pepaslabs/HeadlightRelayControl/github media/Clipboard08.png

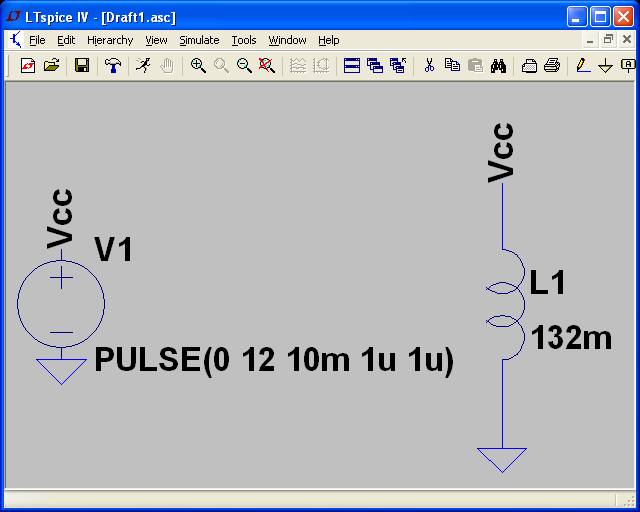
github media/Clipboard08.png
