pepaslabs/HeadlightRelayControl/github media/Clipboard13.png

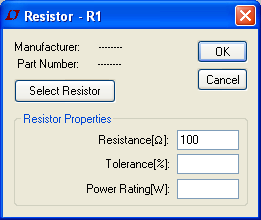
github media/Clipboard13.png
