pepaslabs/HeadlightRelayControl/github media/Clipboard30.png

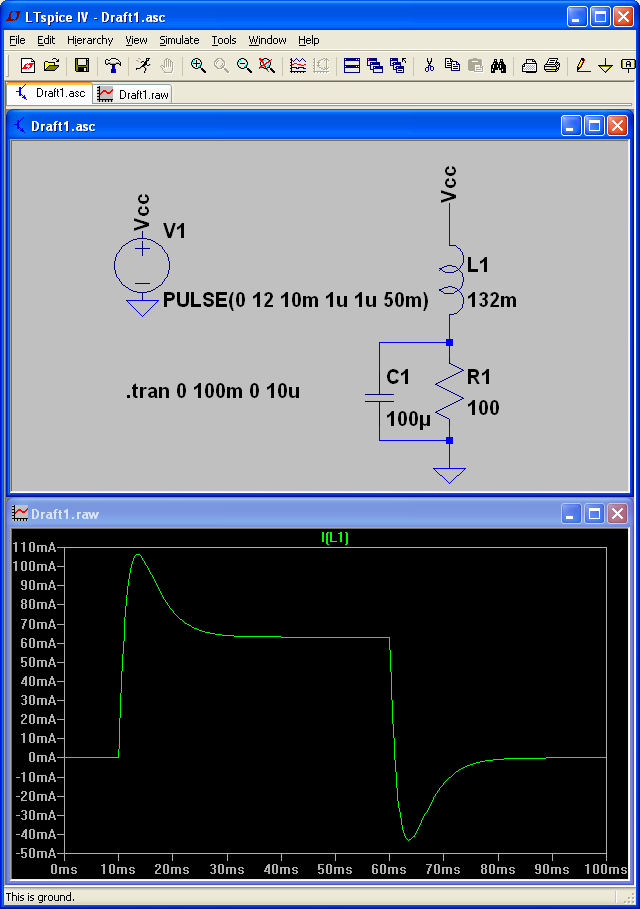
github media/Clipboard30.png
