pepaslabs/HeadlightRelayControl/github media/Clipboard39.png

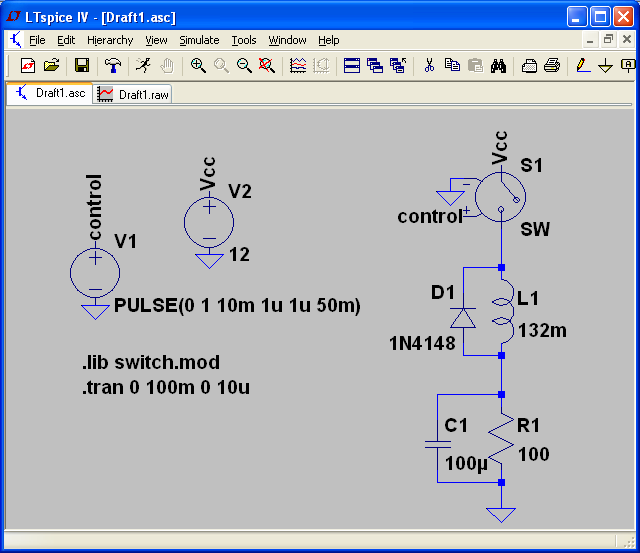
github media/Clipboard39.png
