pepaslabs/HeadlightRelayControl/github media/Photo Mar 18, 10 02 26 PM.jpg

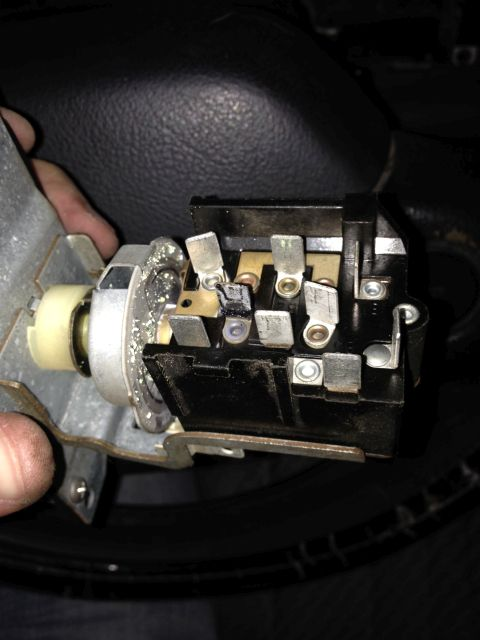
github media/Photo Mar 18, 10 02 26 PM.jpg
