pepaslabs/HeadlightRelayControl/github media/Photo Mar 18, 10 09 22 PM.jpg

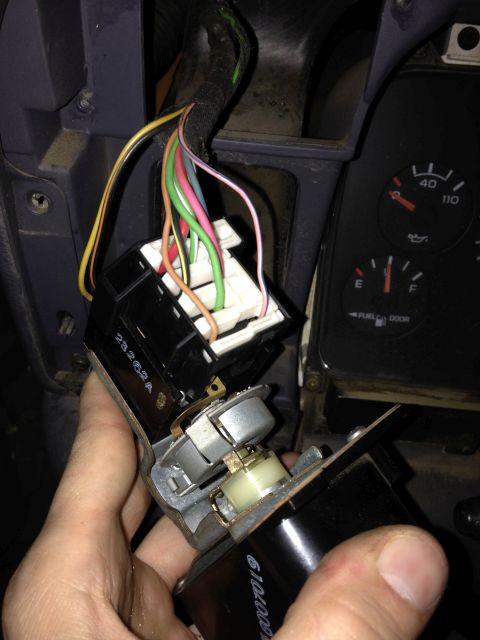
github media/Photo Mar 18, 10 09 22 PM.jpg
