pepaslabs/HeadlightRelayControl/ltspice/Draft1.asc

C1: cap; 100µ; Rser=100m
C2: cap; 100µ; Rser=100m
D1: diode; 1N4148
D2: diode; 1N4148
D3: diode; 1N4148
D4: diode; 1N4148
D5: diode; 1N4148
L1: ind; 132m; Rser=90
L2: ind; 132m; Rser=90
R1: res; 100
R2: res; 100
S1: sw
S2: sw
V1: voltage; PULSE(0 1 20m 1u 1u 40m)
V2: voltage; 14.2
V3: voltage; PULSE(0 1 10m 1u 1u 20m)
Named nets: 0, Vcc, LB_power, HB_power, LB_control, HB_control
.tran 0 100m 0 10u
.lib switch.mod
